Emilien-Wolff/Protorob/Photos/IMG_2800.JPG

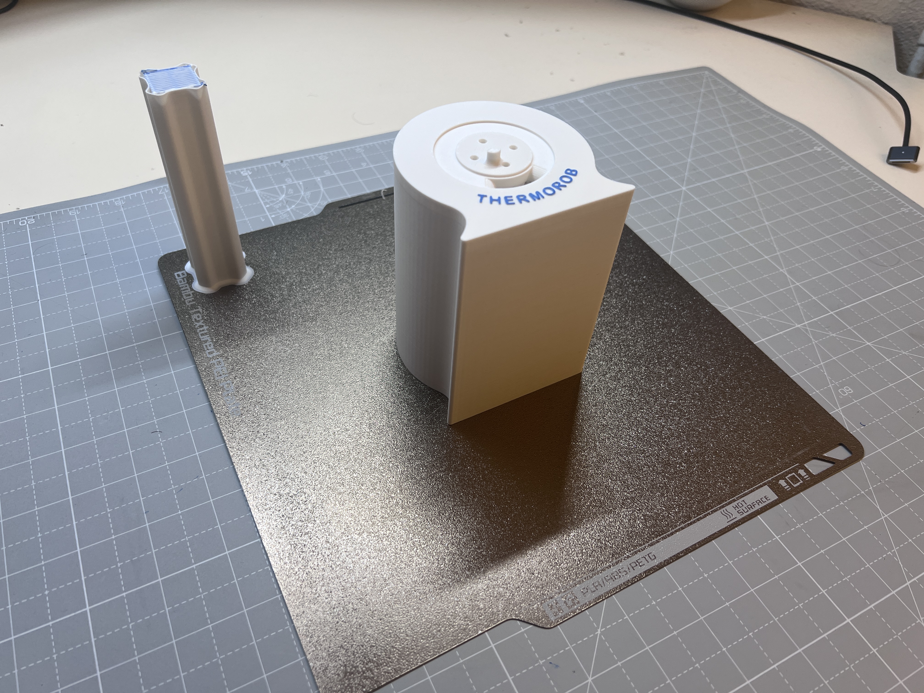
Photos/IMG_2800.JPG
