Emilien-Wolff/Protorob/Photos/IMG_2820.JPG

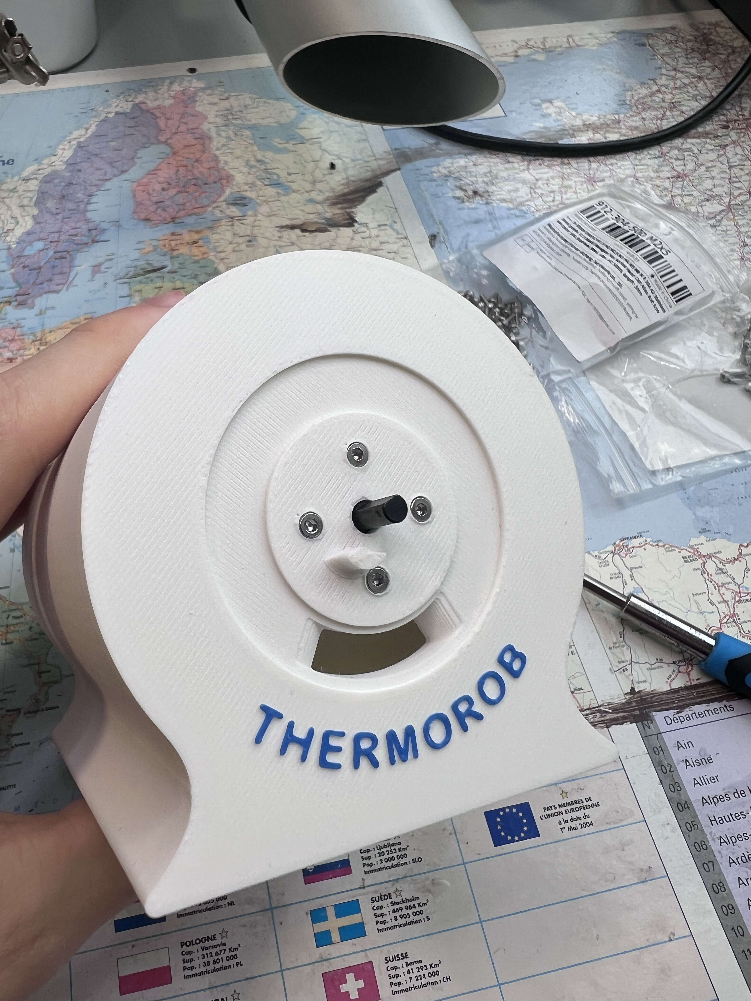
Photos/IMG_2820.JPG
