Emilien-Wolff/Protorob/Photos/IMG_2823.JPG

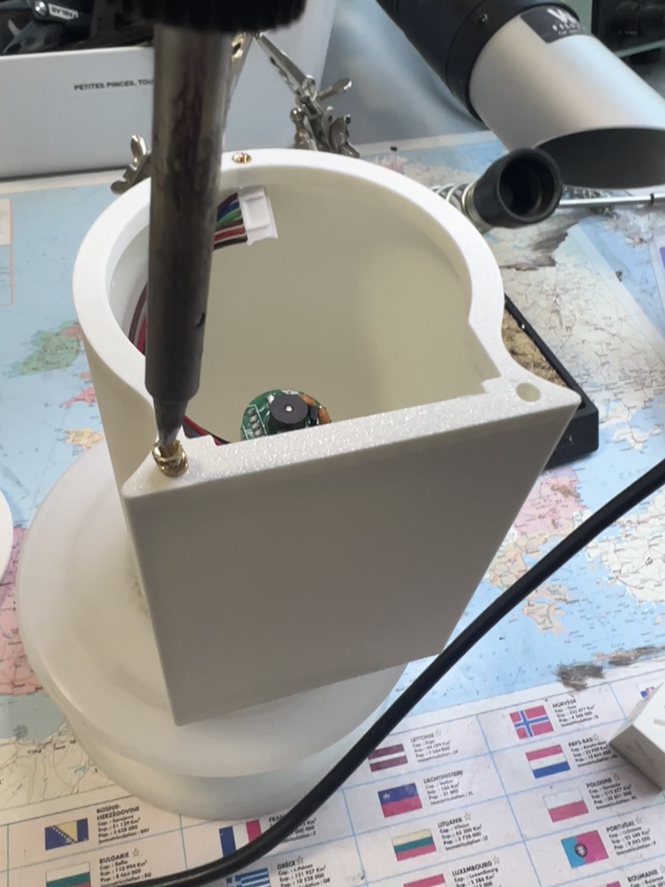
Photos/IMG_2823.JPG
