Emilien-Wolff/Protorob/Photos/WhatsApp Image 2026-01-16 at 12.44.59.jpeg

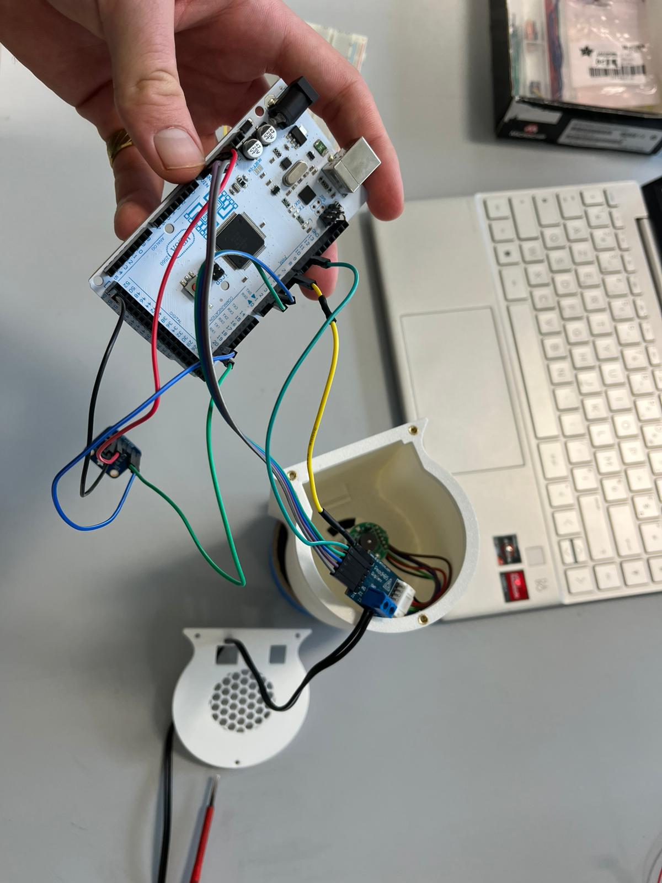
Photos/WhatsApp Image 2026-01-16 at 12.44.59.jpeg
